mathieupommery/LABUBU_IA/HARDWARE/PCB/LIB_KIKAD/libloader/SM10B-SRSS-TB_LF__SN_.stp

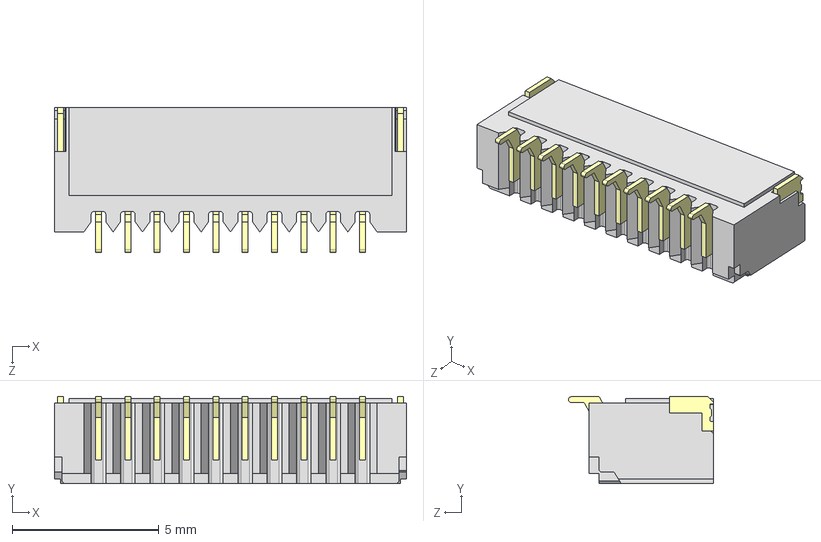
[picture p16: CAD file, 2025-12-20]
HARDWARE/PCB/LIB_KIKAD/libloader/SM10B-SRSS-TB_LF__SN_.stp
12.0 x 2.97 x 4.95 mm
