mathieupommery/LABUBU_IA/HARDWARE/PCB/LIB_KIKAD/libloader/TLE5012BE3005XUMA1.stp

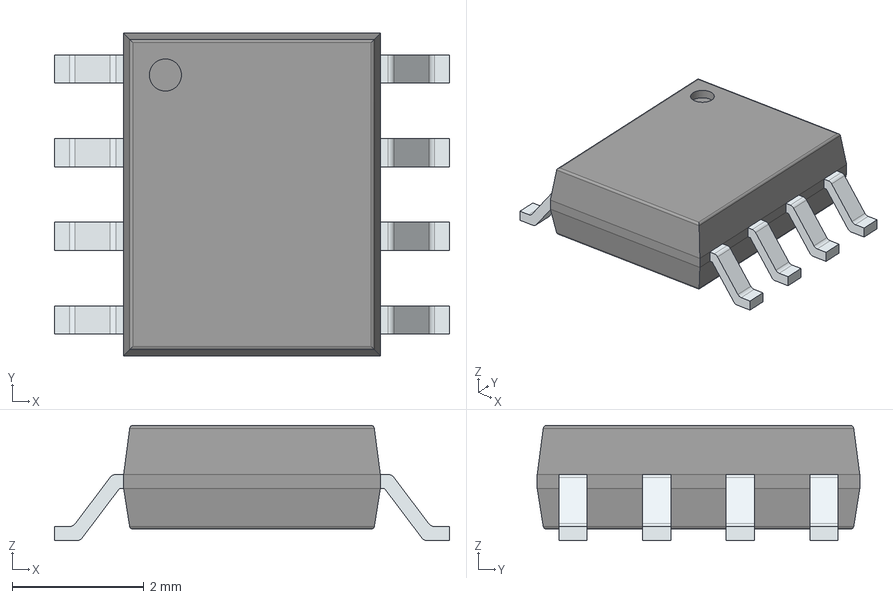
[picture p17: CAD file, 2025-12-20]
HARDWARE/PCB/LIB_KIKAD/libloader/TLE5012BE3005XUMA1.stp
6.00 x 4.90 x 1.75 mm
PinsArrayLR
