mathieupommery/LABUBU_IA/HARDWARE/PCB/LIB_KIKAD/libloader/ESP32-S3FH4R2.stp

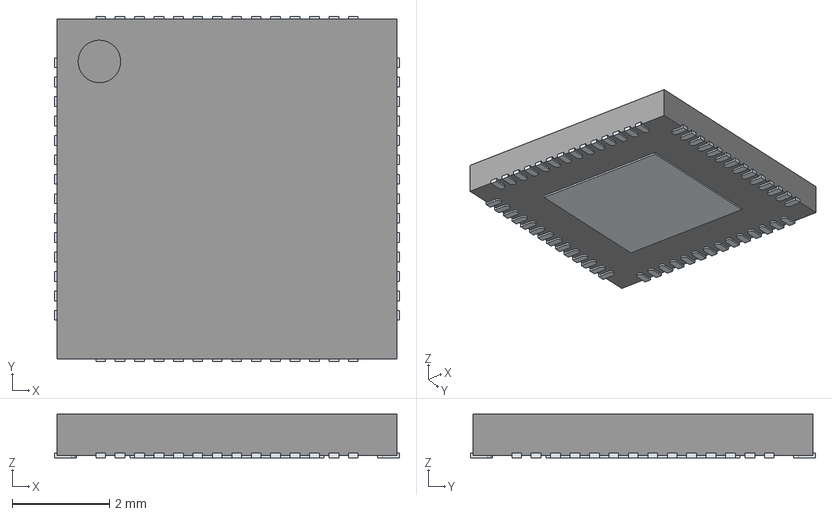
[picture p18: CAD file, 2025-12-20]
HARDWARE/PCB/LIB_KIKAD/libloader/ESP32-S3FH4R2.stp
7.10 x 7.10 x 0.9 mm
ThermalPin
PinsArrayLR
PinsArrayTB
