mathieupommery/LABUBU_IA/HARDWARE/PCB/LIB_KIKAD/libloader/XT30PW-M.stp

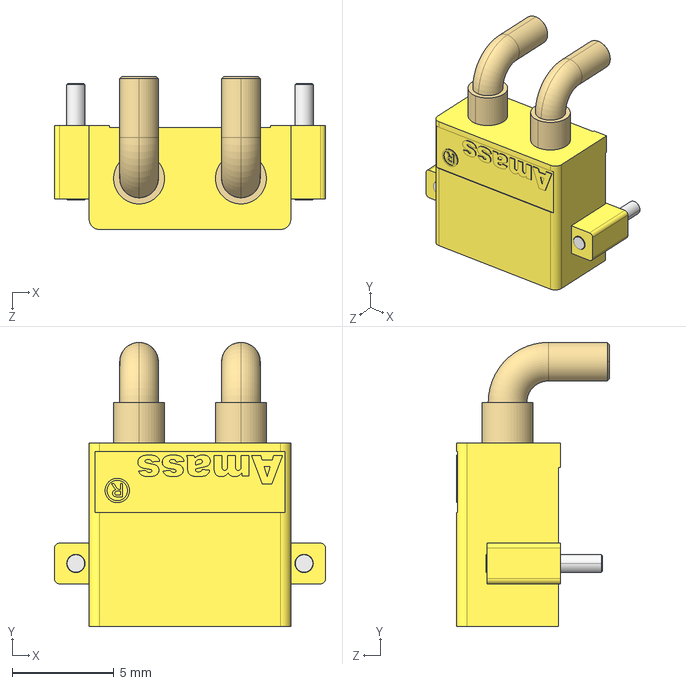
[picture p19: CAD file, 2025-12-20]
HARDWARE/PCB/LIB_KIKAD/libloader/XT30PW-M.stp
13.3 x 13.9 x 7.50 mm
