mathieupommery/LABUBU_IA/HARDWARE/PCB/LIB_KIKAD/libloader/MA330GQ-Z.stp

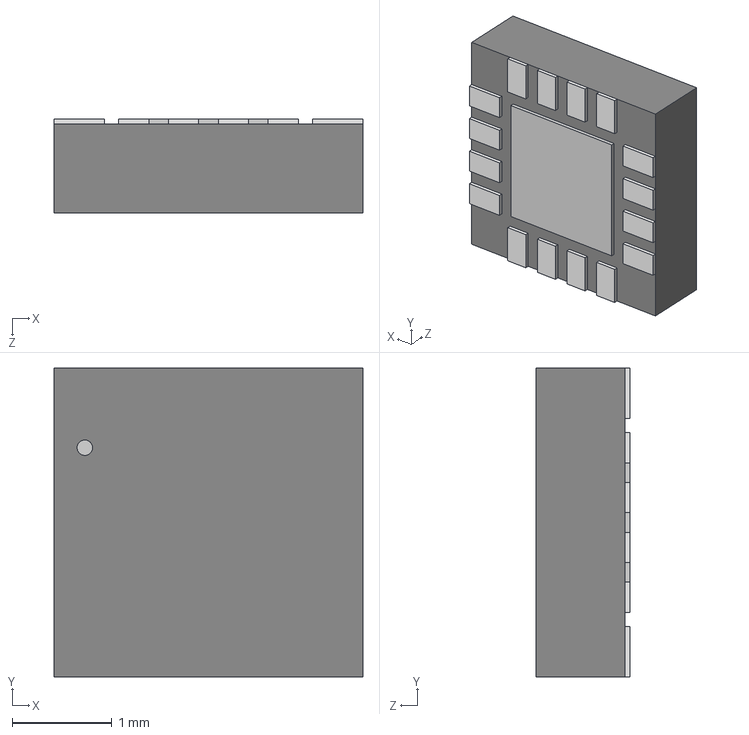
[picture p20: CAD file, 2025-12-20]
HARDWARE/PCB/LIB_KIKAD/libloader/MA330GQ-Z.stp
3.10 x 3.10 x 0.942 mm
