mathieupommery/LABUBU_IA/HARDWARE/PCB/LIB_KIKAD/libloader/BSS138PW.stp

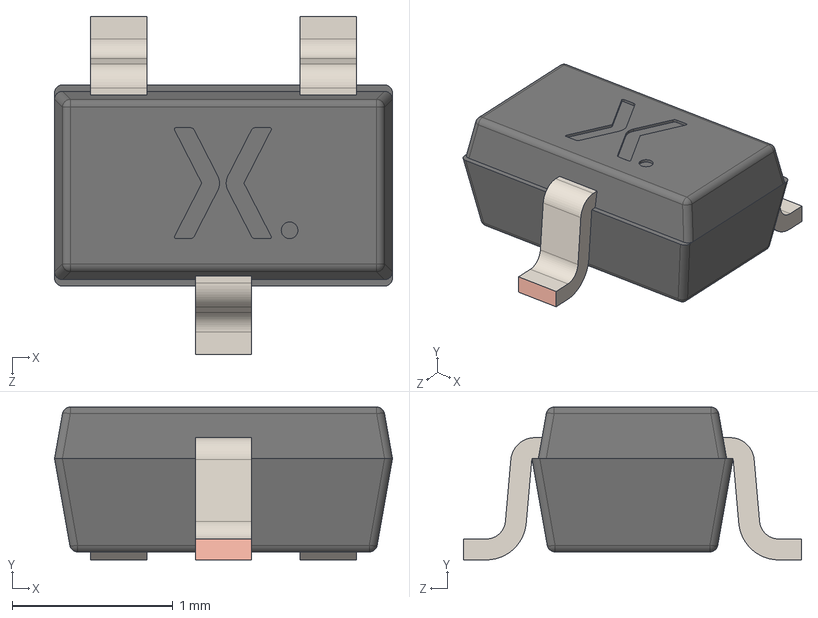
[picture p21: CAD file, 2025-12-20]
HARDWARE/PCB/LIB_KIKAD/libloader/BSS138PW.stp
2.10 x 0.95 x 2.10 mm
Upper body
lower body
Lead x 3
