mathieupommery/LABUBU_IA/HARDWARE/PCB/LIB_KIKAD/libloader/SM05B-GHS-TB_LF__SN_.stp

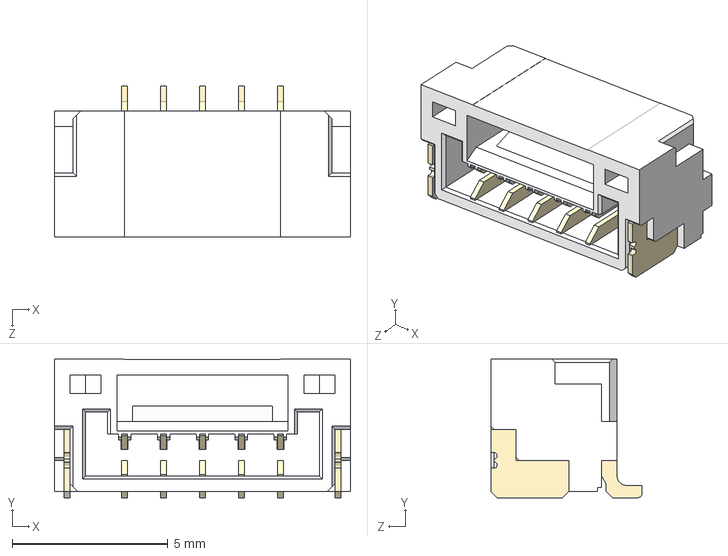
[picture p22: CAD file, 2025-12-20]
HARDWARE/PCB/LIB_KIKAD/libloader/SM05B-GHS-TB_LF__SN_.stp
9.50 x 4.45 x 4.85 mm
