mathieupommery/LABUBU_IA/HARDWARE/PCB/LIB_KIKAD/libloader/TPSM828214SILR.stp

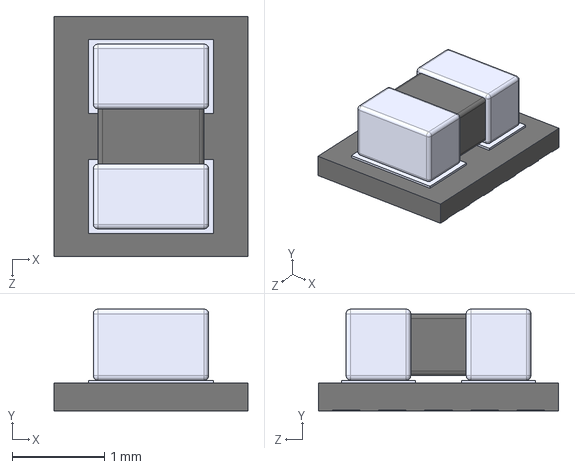
[picture p23: CAD file, 2025-12-20]
HARDWARE/PCB/LIB_KIKAD/libloader/TPSM828214SILR.stp
2.10 x 1.10 x 2.60 mm
