mathieupommery/LABUBU_IA/HARDWARE/PCB/LIB_KIKAD/libloader/HMC5883L-TR.stp

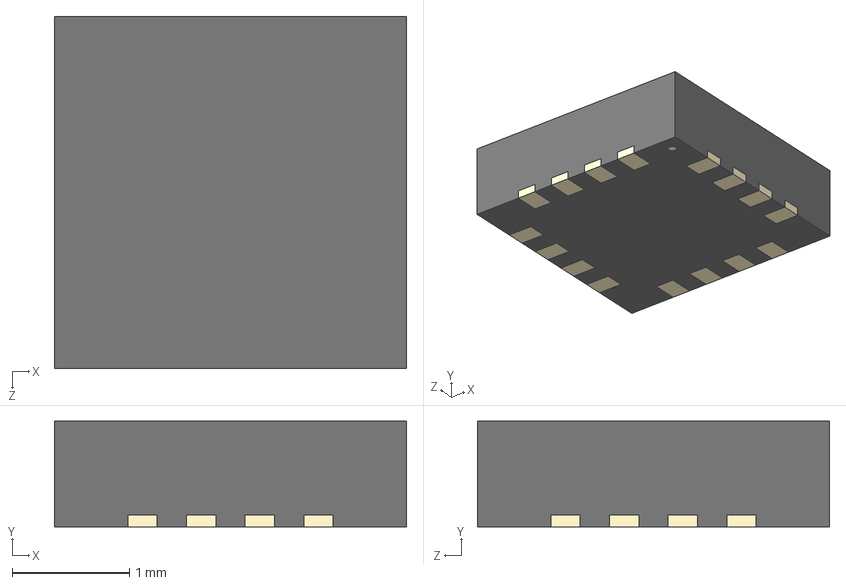
[picture p24: CAD file, 2025-12-20]
HARDWARE/PCB/LIB_KIKAD/libloader/HMC5883L-TR.stp
3.00 x 0.9 x 3.00 mm
