mathieupommery/LABUBU_IA/HARDWARE/PCB/LIB_KIKAD/libloader/LFXTAL069527REEL.stp

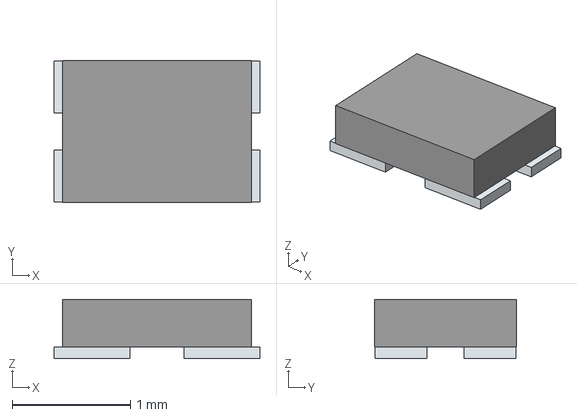
[picture p25: CAD file, 2025-12-20]
HARDWARE/PCB/LIB_KIKAD/libloader/LFXTAL069527REEL.stp
1.74 x 1.20 x 0.5 mm
Pins
