mathieupommery/LABUBU_IA/HARDWARE/PCB/LIB_KIKAD/libloader/LM2775DSGT.stp

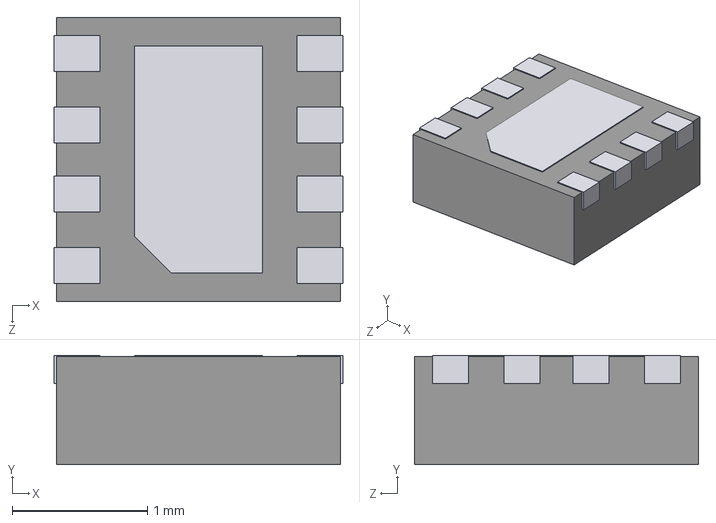
[picture p26: CAD file, 2025-12-20]
HARDWARE/PCB/LIB_KIKAD/libloader/LM2775DSGT.stp
2.14 x 0.81 x 2.10 mm
