mathieupommery/LABUBU_IA/HARDWARE/PCB/LIB_KIKAD/libloader/MAX-M10S-00B.stp

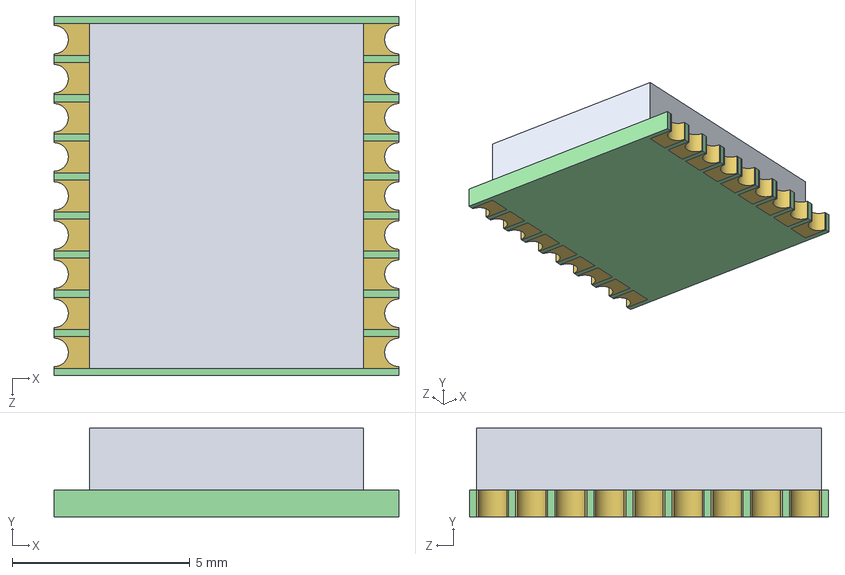
[picture p27: CAD file, 2025-12-20]
HARDWARE/PCB/LIB_KIKAD/libloader/MAX-M10S-00B.stp
9.70 x 2.50 x 10.1 mm
