mathieupommery/LABUBU_IA/HARDWARE/PCB/LIB_KIKAD/libloader/XT60PW-M.stp

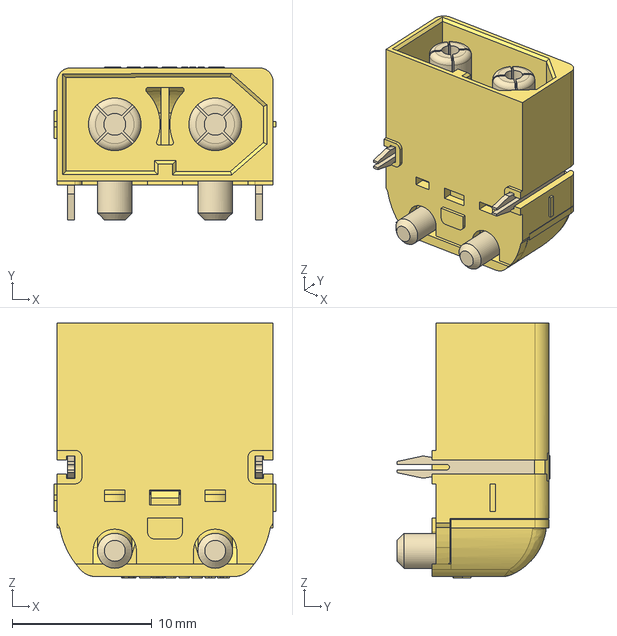
[picture p28: CAD file, 2025-12-20]
HARDWARE/PCB/LIB_KIKAD/libloader/XT60PW-M.stp
15.9 x 10.9 x 18.3 mm
