mathieupommery/LABUBU_IA/HARDWARE/PCB/LIB_KIKAD/libloader/MPX1D1264L4R7.stp

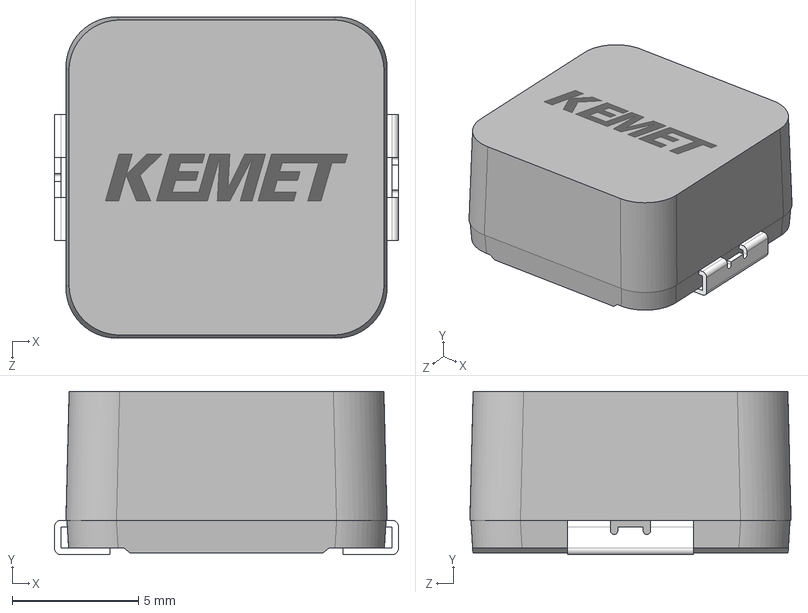
[picture p29: CAD file, 2025-12-20]
HARDWARE/PCB/LIB_KIKAD/libloader/MPX1D1264L4R7.stp
13.6 x 6.46 x 12.7 mm
