mathieupommery/LABUBU_IA/HARDWARE/PCB/LIB_KIKAD/libloader/STM32G071G8U6.stp

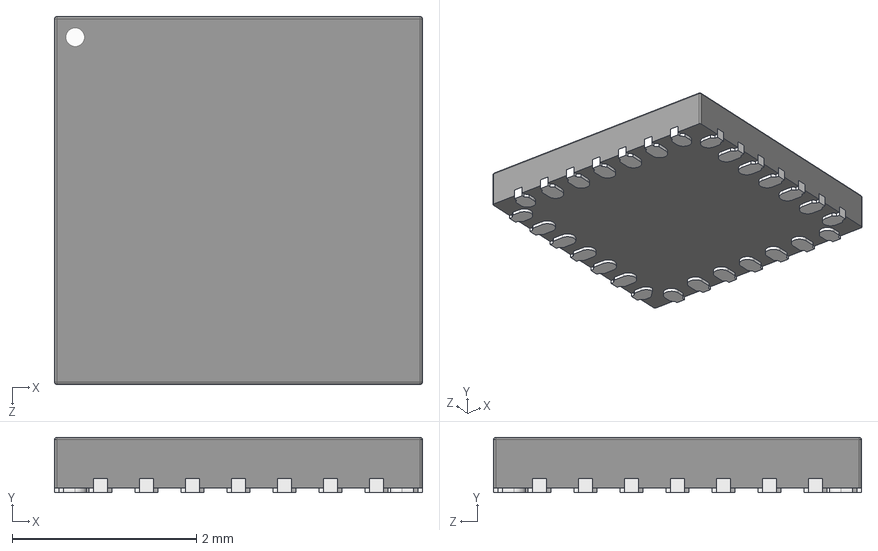
[picture p30: CAD file, 2025-12-20]
HARDWARE/PCB/LIB_KIKAD/libloader/STM32G071G8U6.stp
4.00 x 0.601 x 4.00 mm
