mathieupommery/LABUBU_IA/HARDWARE/PCB/LIB_KIKAD/libloader/SQS401EN-T1_BE3.stp

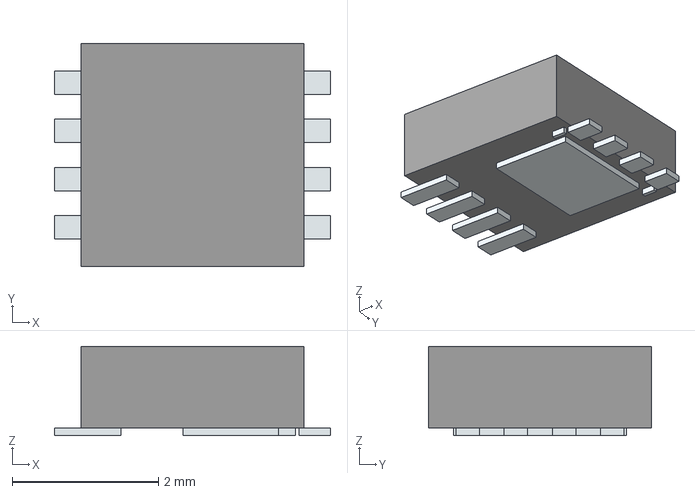
[picture p31: CAD file, 2025-12-20]
HARDWARE/PCB/LIB_KIKAD/libloader/SQS401EN-T1_BE3.stp
3.78 x 3.05 x 1.22 mm
Pins
