mathieupommery/LABUBU_IA/HARDWARE/PCB/LIB_KIKAD/libloader/W25Q16JWXHIQ_TR.stp

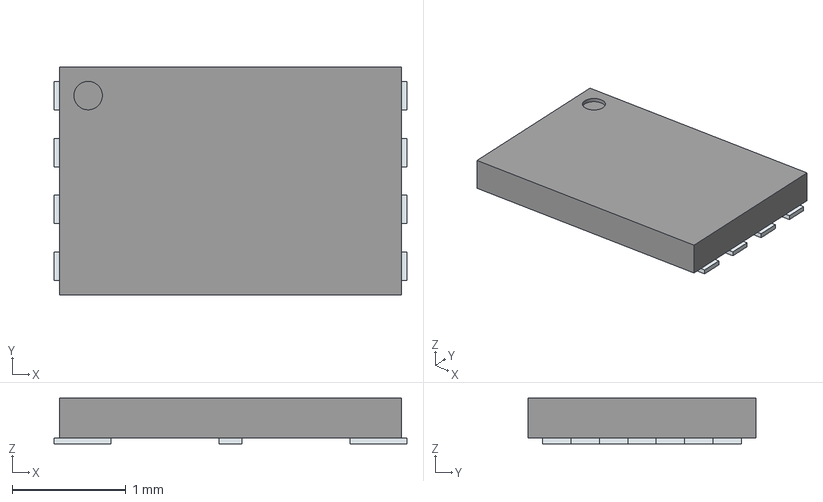
[picture p32: CAD file, 2025-12-20]
HARDWARE/PCB/LIB_KIKAD/libloader/W25Q16JWXHIQ_TR.stp
3.10 x 2.00 x 0.4 mm
ThermalPin
PinsArrayLR
