mathieupommery/LABUBU_IA/HARDWARE/PCB/LIB_KIKAD/libloader/STSPIN32G0A2.stp

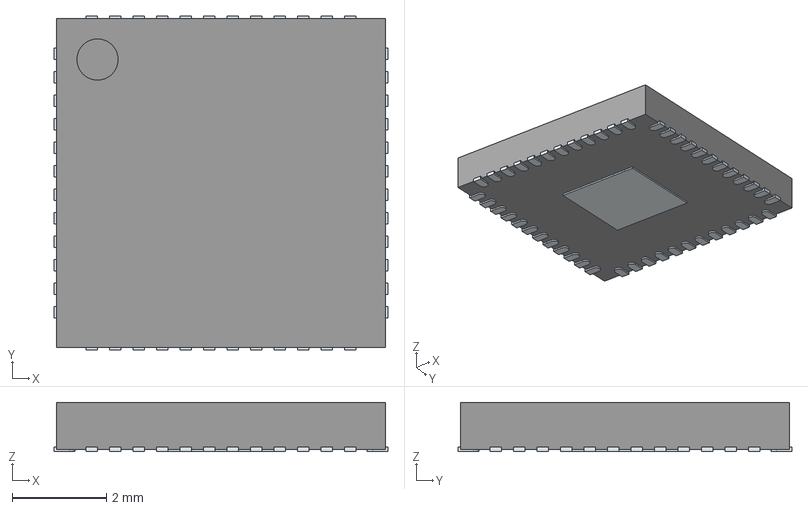
[picture p33: CAD file, 2025-12-20]
HARDWARE/PCB/LIB_KIKAD/libloader/STSPIN32G0A2.stp
7.10 x 7.10 x 1.05 mm
ThermalPin
PinsArrayLR
PinsArrayTB
