mathieupommery/LABUBU_IA/HARDWARE/PCB/LIB_KIKAD/libloader/CSTNE8M00GH5C000R0.stp

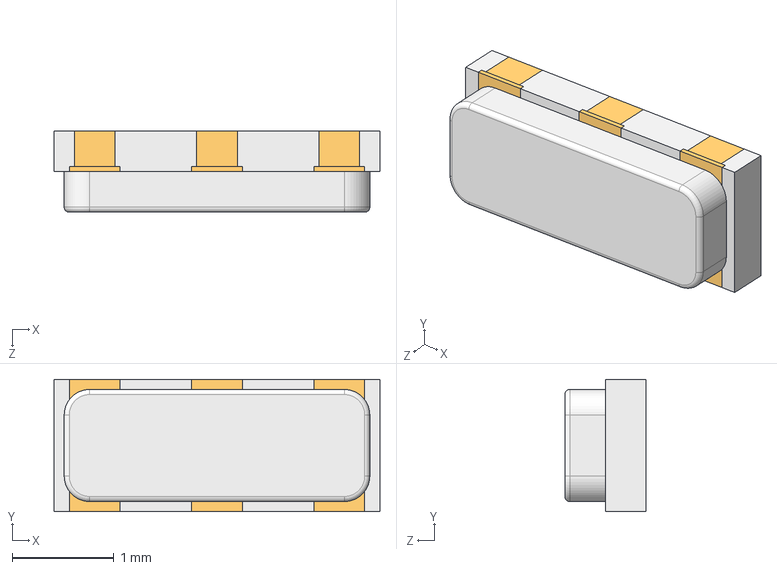
[picture p34: CAD file, 2025-12-20]
HARDWARE/PCB/LIB_KIKAD/libloader/CSTNE8M00GH5C000R0.stp
3.20 x 1.30 x 0.8 mm
