mathieupommery/LABUBU_IA/HARDWARE/PCB/LIB_KIKAD/libloader/TS5A3159ADCKR.stp

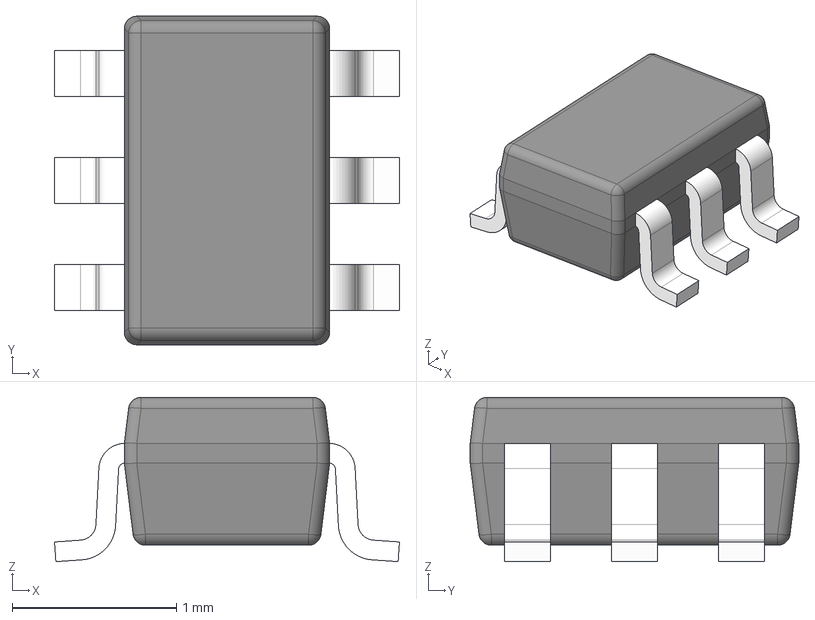
[picture p35: CAD file, 2025-12-20]
HARDWARE/PCB/LIB_KIKAD/libloader/TS5A3159ADCKR.stp
2.10 x 2.00 x 1.00 mm
BODY-SOT
LEAD-SOT x 6
PIN1-ID
