mathieupommery/LABUBU_IA/HARDWARE/PCB/LIB_KIKAD/libloader/STR2N2VH5.stp

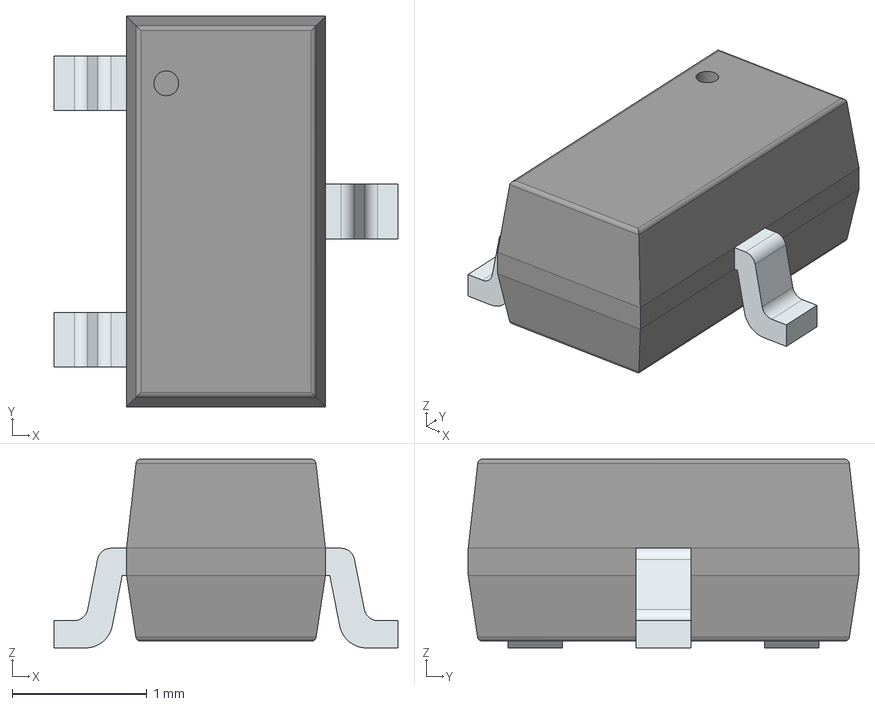
[picture p36: CAD file, 2025-12-20]
HARDWARE/PCB/LIB_KIKAD/libloader/STR2N2VH5.stp
2.55 x 2.90 x 1.40 mm
PinsArrayL
FilletPinR
