mathieupommery/LABUBU_IA/HARDWARE/PCB/LIB_KIKAD/libloader/DMT6018LDR-7.stp

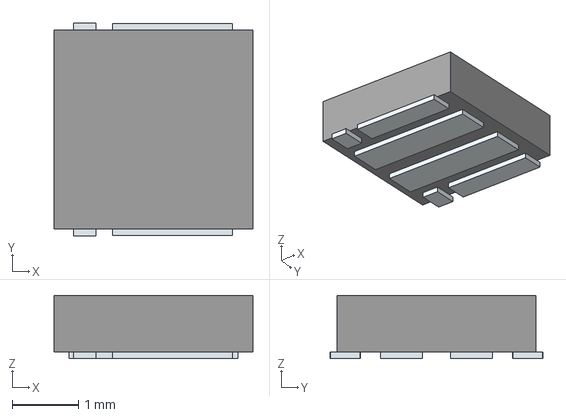
[picture p37: CAD file, 2025-12-20]
HARDWARE/PCB/LIB_KIKAD/libloader/DMT6018LDR-7.stp
3.00 x 3.22 x 0.95 mm
Pins
