mathieupommery/LABUBU_IA/HARDWARE/PCB/LIB_KIKAD/libloader/BAT60JFILM.stp

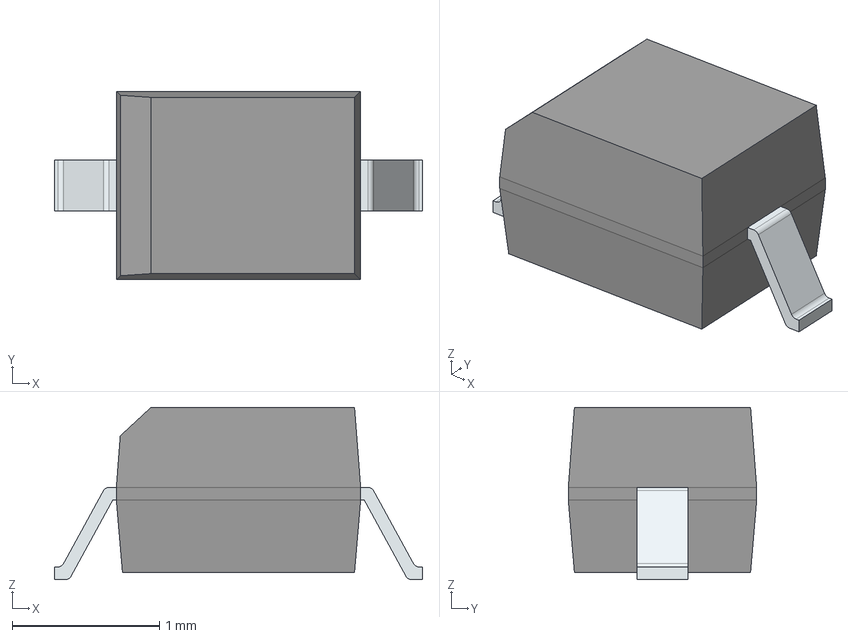
[picture p38: CAD file, 2025-12-20]
HARDWARE/PCB/LIB_KIKAD/libloader/BAT60JFILM.stp
2.50 x 1.28 x 1.17 mm
FilletPinL
FilletPinR
