mathieupommery/LABUBU_IA/HARDWARE/PCB/LIB_KIKAD/libloader/SM02B-GHS-TB_LF__SN_.stp

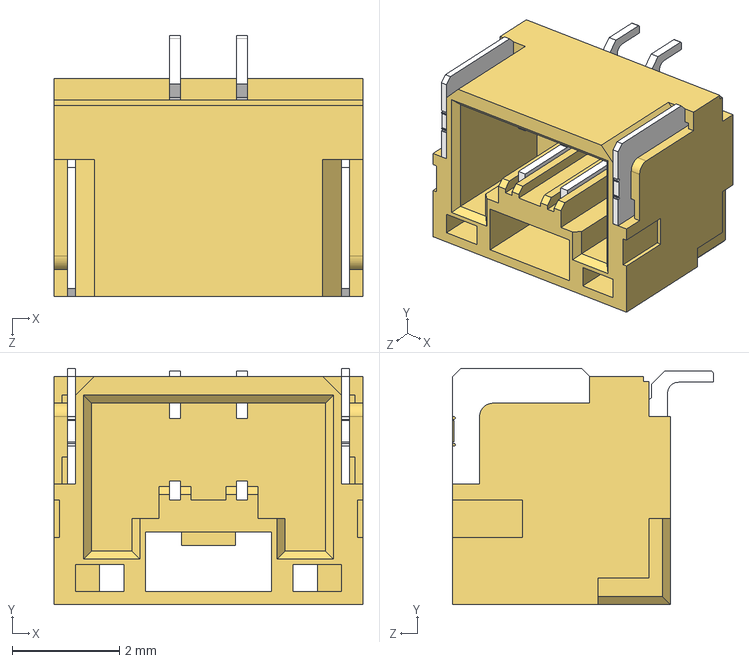
[picture p39: CAD file, 2025-12-20]
HARDWARE/PCB/LIB_KIKAD/libloader/SM02B-GHS-TB_LF__SN_.stp
5.75 x 4.40 x 4.85 mm
