mathieupommery/LABUBU_IA/HARDWARE/PCB/LIB_KIKAD/libloader/DPS368XTSA1.stp

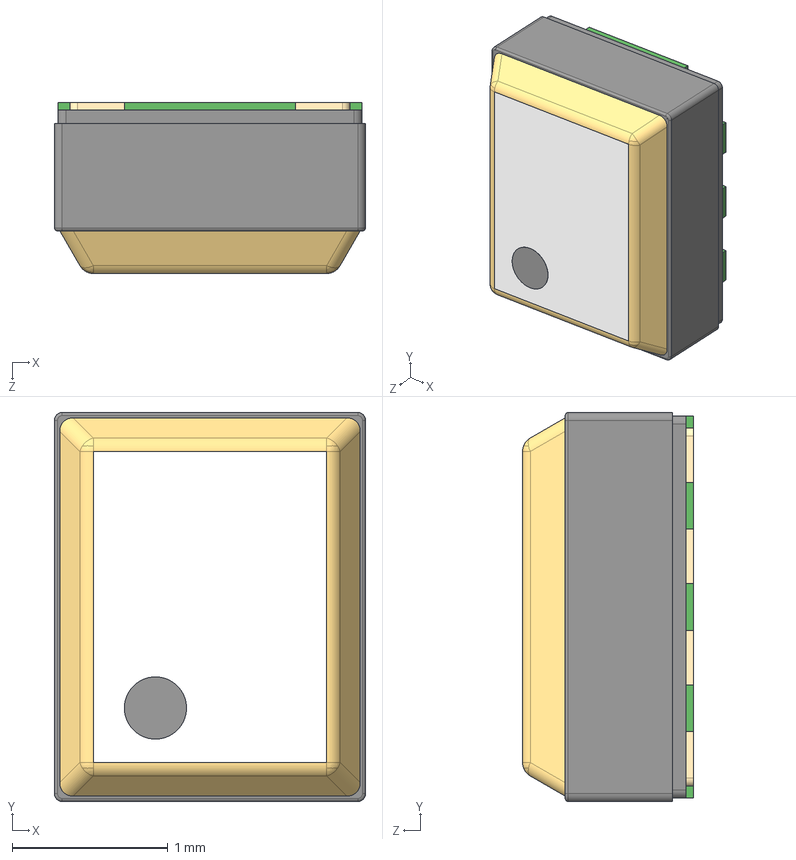
[picture p40: CAD file, 2025-12-20]
HARDWARE/PCB/LIB_KIKAD/libloader/DPS368XTSA1.stp
2.00 x 2.50 x 1.10 mm
Notch
Infineon Logo Adjustable_5
