mathieupommery/LABUBU_IA/HARDWARE/PCB/LIB_KIKAD/libloader/NC7WZ07P6X.stp

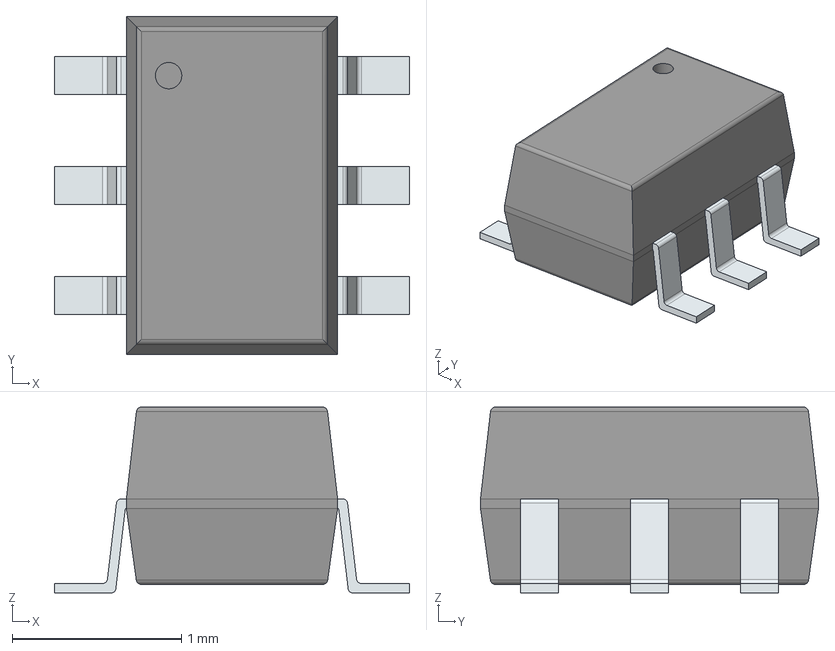
[picture p41: CAD file, 2025-12-20]
HARDWARE/PCB/LIB_KIKAD/libloader/NC7WZ07P6X.stp
2.10 x 2.00 x 1.10 mm
PinsArrayLR
