mathieupommery/LABUBU_IA/HARDWARE/PCB/LIB_KIKAD/libloader/STG719STR.stp

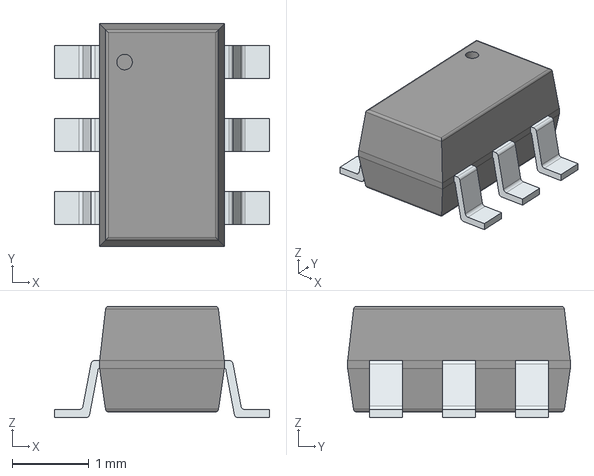
[picture p42: CAD file, 2025-12-20]
HARDWARE/PCB/LIB_KIKAD/libloader/STG719STR.stp
2.80 x 2.90 x 1.45 mm
PinsArrayLR
