mathieupommery/LABUBU_IA/HARDWARE/PCB/LIB_KIKAD/libloader/ESP32-C6FH4.stp

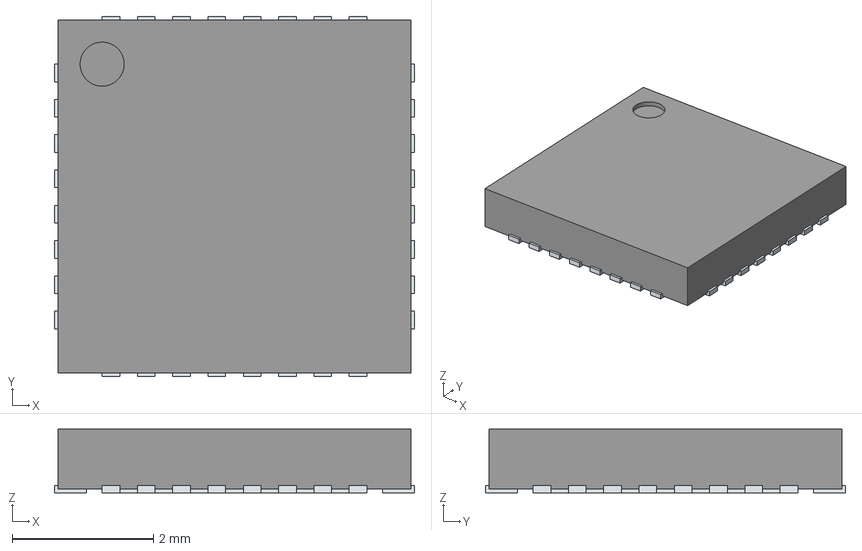
[picture p43: CAD file, 2025-12-20]
HARDWARE/PCB/LIB_KIKAD/libloader/ESP32-C6FH4.stp
5.10 x 5.10 x 0.9 mm
ThermalPin
PinsArrayLR
PinsArrayTB
