mathieupommery/LABUBU_IA/HARDWARE/PCB/LIB_KIKAD/libloader/RCLAMP3521ZATFT.stp

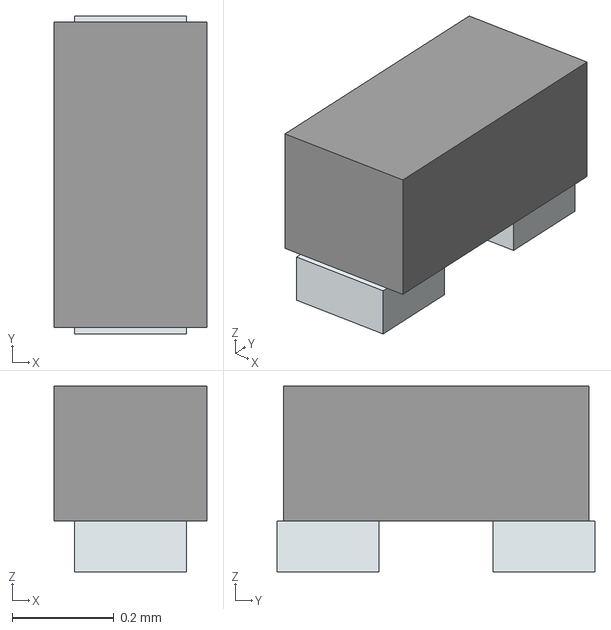
[picture p44: CAD file, 2025-12-20]
HARDWARE/PCB/LIB_KIKAD/libloader/RCLAMP3521ZATFT.stp
0.3 x 0.625 x 0.365 mm
Pins
