mathieupommery/LABUBU_IA/HARDWARE/PCB/LIB_KIKAD/libloader/SM12B-SRSS-TB_LF__SN_.stp

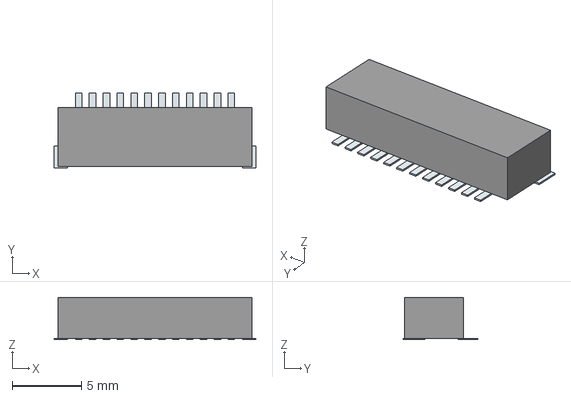
[picture p45: CAD file, 2025-12-20]
HARDWARE/PCB/LIB_KIKAD/libloader/SM12B-SRSS-TB_LF__SN_.stp
14.6 x 5.37 x 3.05 mm
Pins
