mathieupommery/LABUBU_IA/HARDWARE/PCB/LIB_KIKAD/libloader/W25N01GVZEIT.stp

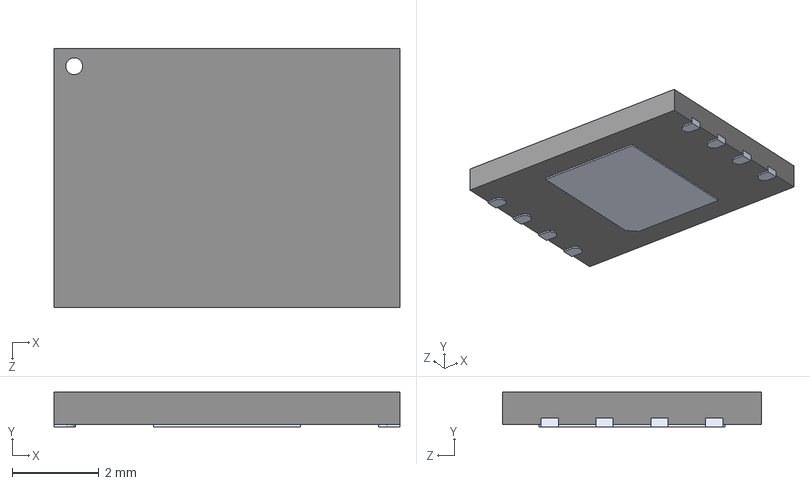
[picture p46: CAD file, 2025-12-20]
HARDWARE/PCB/LIB_KIKAD/libloader/W25N01GVZEIT.stp
8.00 x 0.8 x 6.00 mm
