mathieupommery/LABUBU_IA/HARDWARE/PCB/LIB_KIKAD/libloader/LSM6DSV80XTR.stp

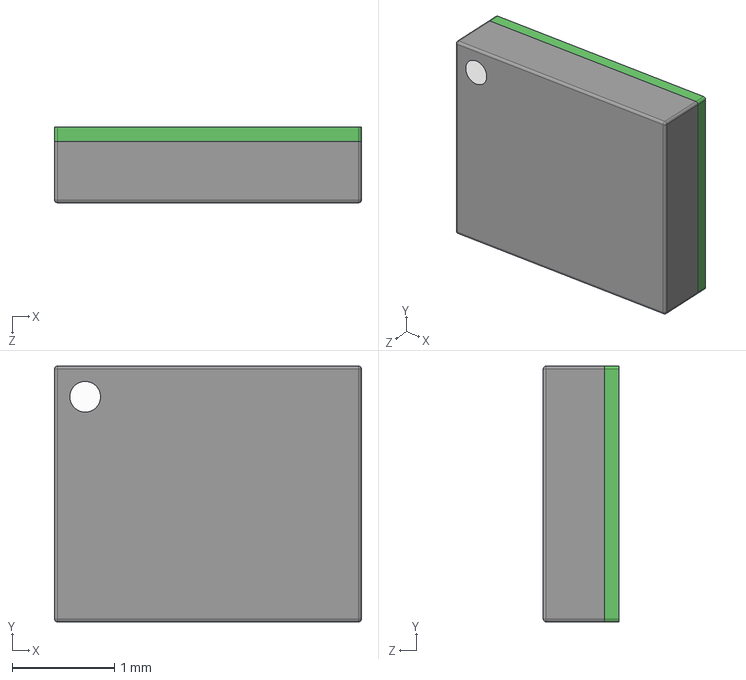
[picture p47: CAD file, 2025-12-20]
HARDWARE/PCB/LIB_KIKAD/libloader/LSM6DSV80XTR.stp
3.00 x 2.50 x 0.74 mm
