mathieupommery/LABUBU_IA/HARDWARE/PCB/LIB_KIKAD/libloader/LTC4065LEDC#TRMPBF.stp

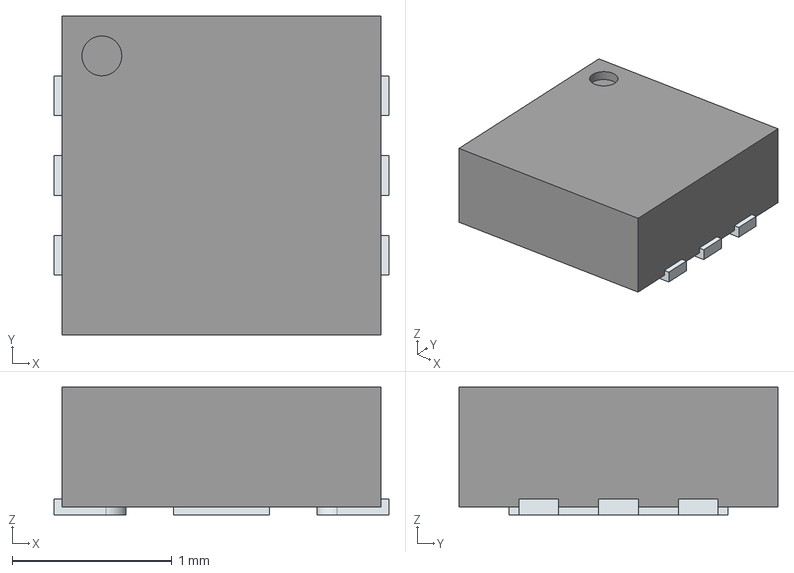
[picture p48: CAD file, 2025-12-20]
HARDWARE/PCB/LIB_KIKAD/libloader/LTC4065LEDC#TRMPBF.stp
2.10 x 2.00 x 0.8 mm
ThermalPin
PinsArrayLR
