mathieupommery/LABUBU_IA/HARDWARE/PCB/LIB_KIKAD/libloader/CHSA3920R0003F.stp

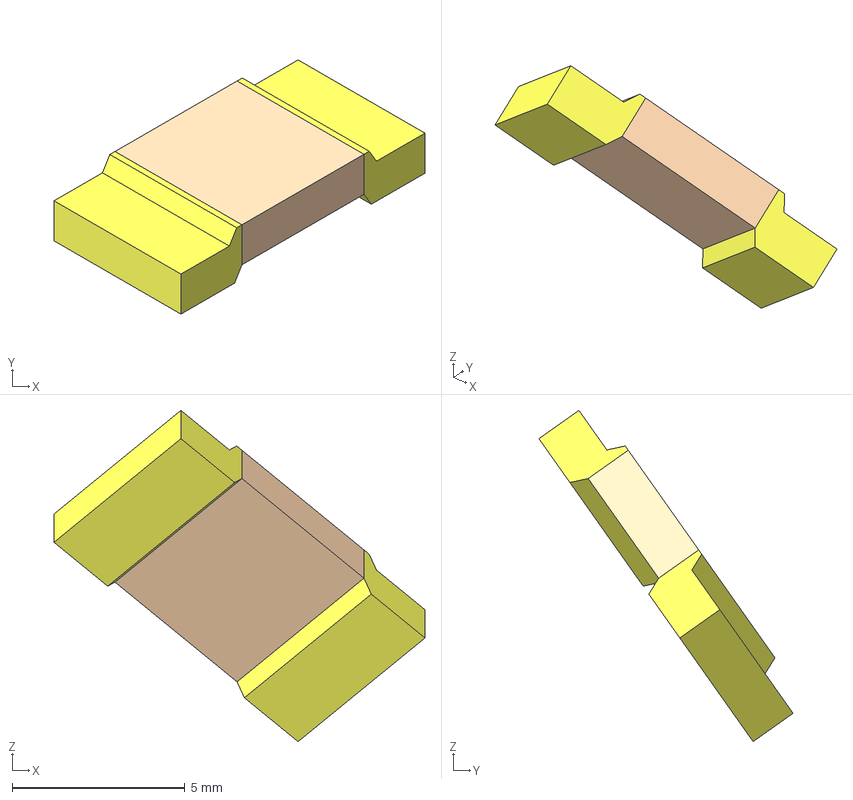
[picture p49: CAD file, 2025-12-20]
HARDWARE/PCB/LIB_KIKAD/libloader/CHSA3920R0003F.stp
10.7 x 7.36 x 9.60 mm
