mathieupommery/LABUBU_IA/HARDWARE/PCB/LIB_KIKAD/libloader/SIA527DJ-T1-GE3.stp

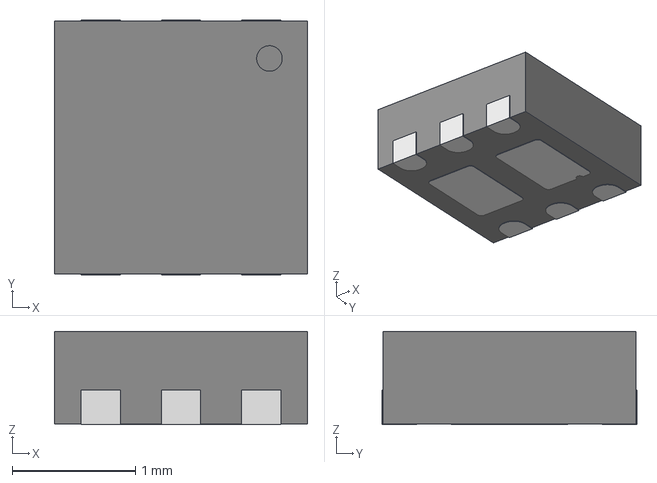
[picture p50: CAD file, 2025-12-20]
HARDWARE/PCB/LIB_KIKAD/libloader/SIA527DJ-T1-GE3.stp
2.05 x 2.07 x 0.757 mm
