mathieupommery/LABUBU_IA/HARDWARE/PCB/LIB_KIKAD/libloader/ICM-42688-P.stp

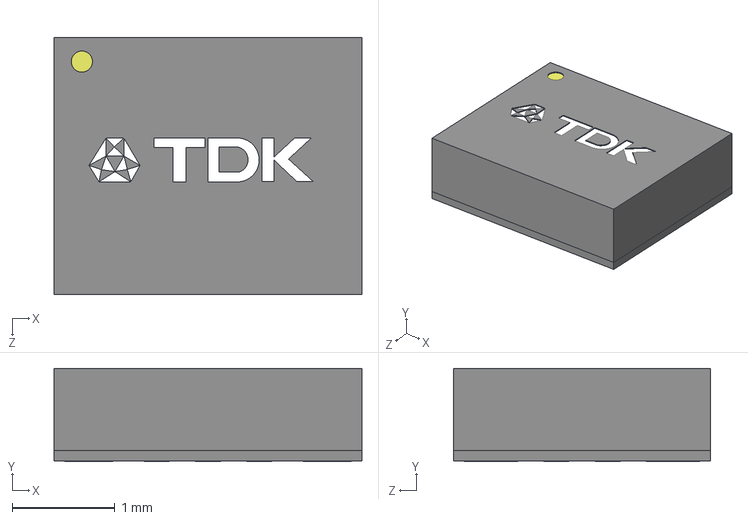
[picture p51: CAD file, 2025-12-20]
HARDWARE/PCB/LIB_KIKAD/libloader/ICM-42688-P.stp
3.00 x 0.91 x 2.50 mm
