mathieupommery/LABUBU_IA/HARDWARE/PCB/LIB_KIKAD/libloader/EMIF06-MSD02N16.stp

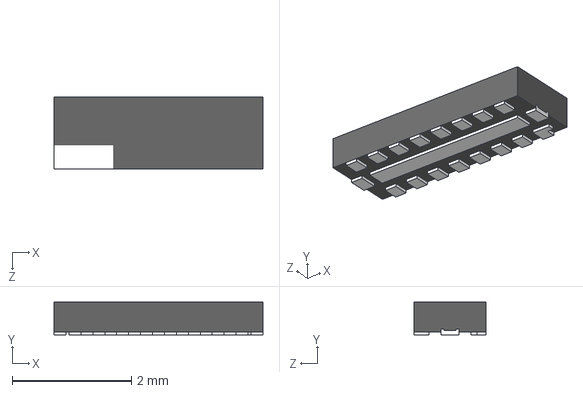
[picture p52: CAD file, 2025-12-20]
HARDWARE/PCB/LIB_KIKAD/libloader/EMIF06-MSD02N16.stp
3.50 x 0.55 x 1.20 mm
