mathieupommery/LABUBU_IA/HARDWARE/PCB/LIB_KIKAD/libloader/SF14-1582M5UUD2.stp

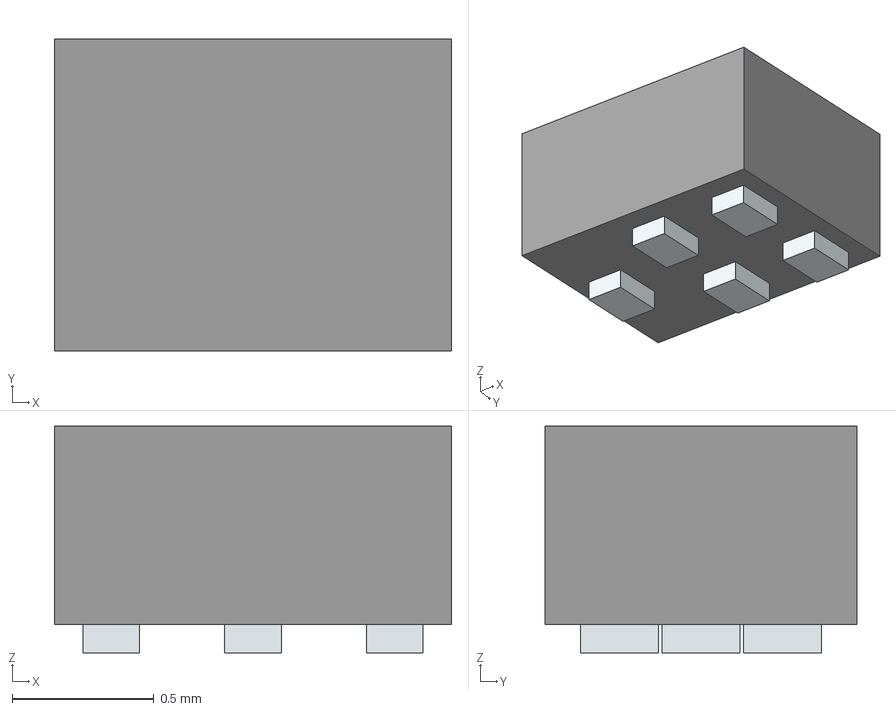
[picture p53: CAD file, 2025-12-20]
HARDWARE/PCB/LIB_KIKAD/libloader/SF14-1582M5UUD2.stp
1.40 x 1.10 x 0.8 mm
Pins
