mathieupommery/LABUBU_IA/HARDWARE/PCB/LIB_KIKAD/libloader/MIA-M10Q-00B.stp

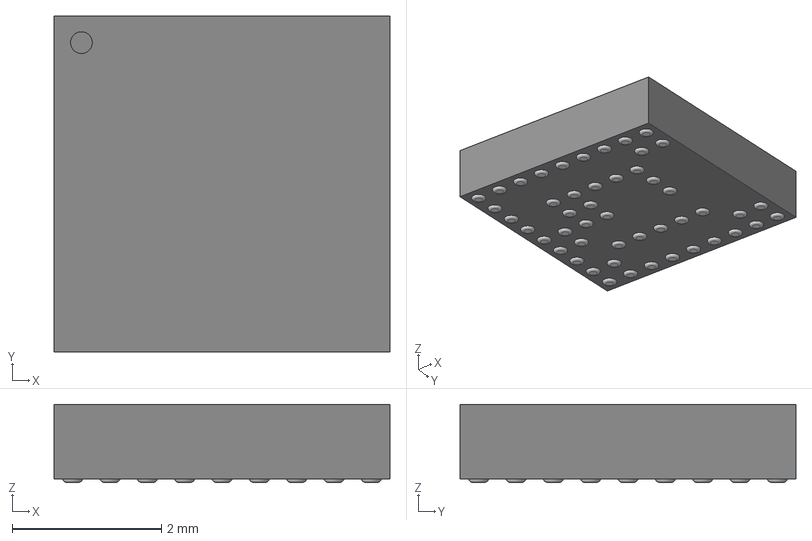
[picture p54: CAD file, 2025-12-20]
HARDWARE/PCB/LIB_KIKAD/libloader/MIA-M10Q-00B.stp
4.50 x 4.50 x 1.04 mm
