mathieupommery/LABUBU_IA/HARDWARE/PCB/LIB_KIKAD/libloader/BMP581.stp

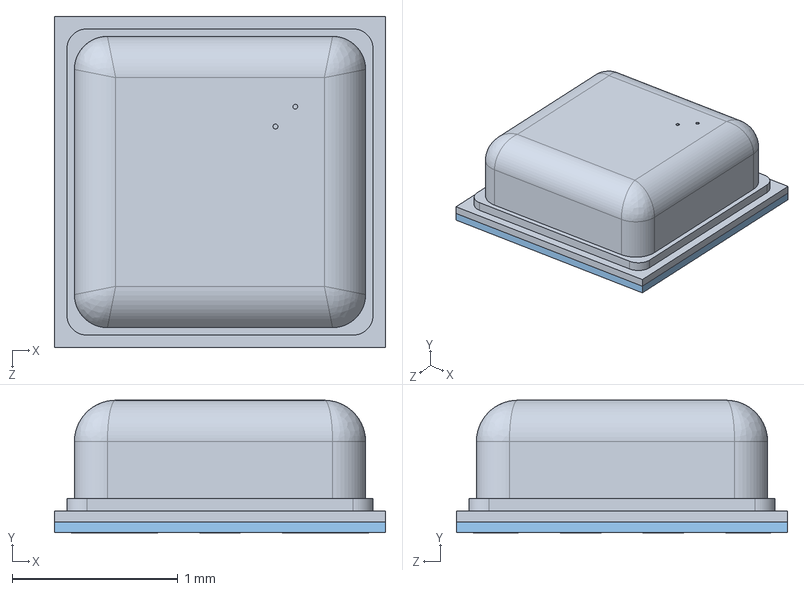
[picture p55: CAD file, 2025-12-20]
HARDWARE/PCB/LIB_KIKAD/libloader/BMP581.stp
2.00 x 0.801 x 2.00 mm
