mathieupommery/LABUBU_IA/HARDWARE/PCB/LIB_KIKAD/libloader/TPS3424A11C13ADRLR.stp

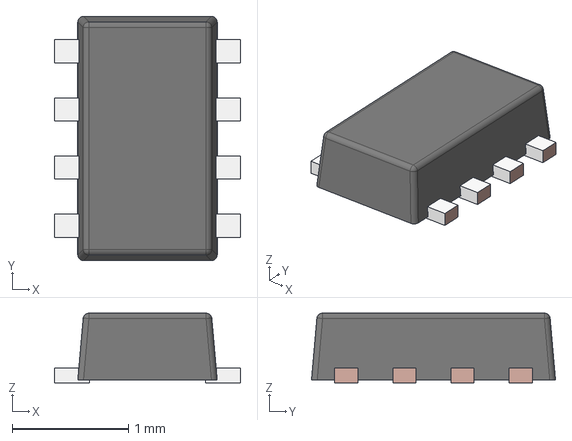
[picture p56: CAD file, 2025-12-20]
HARDWARE/PCB/LIB_KIKAD/libloader/TPS3424A11C13ADRLR.stp
1.60 x 2.10 x 0.6 mm
FRAME-DRL0008A
BODY-SOT
