mathieupommery/LABUBU_IA/HARDWARE/PCB/LIB_KIKAD/libloader/LTC2955CDDB-2#TRMPBF.stp

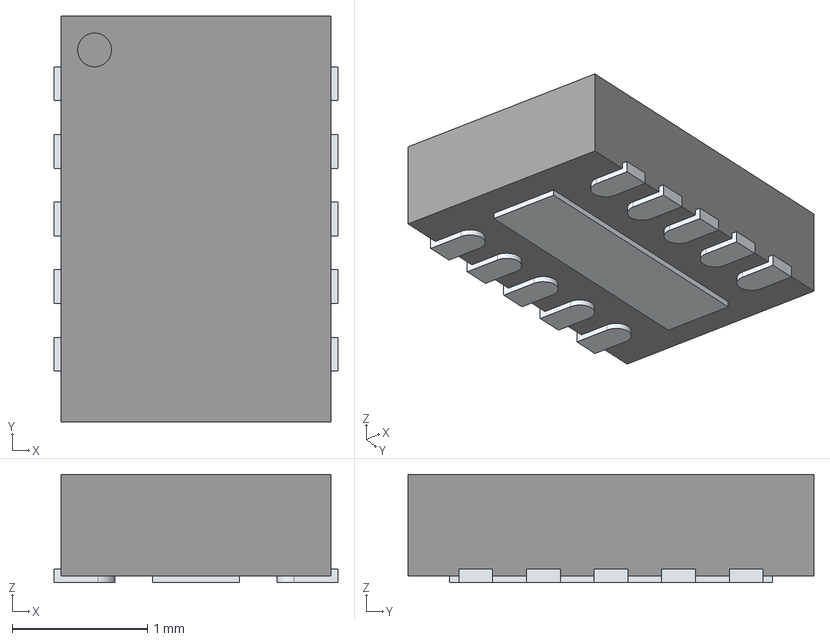
[picture p57: CAD file, 2025-12-20]
HARDWARE/PCB/LIB_KIKAD/libloader/LTC2955CDDB-2#TRMPBF.stp
2.10 x 3.00 x 0.8 mm
ThermalPin
PinsArrayLR
