mathieupommery/LABUBU_IA/HARDWARE/PCB/LIB_KIKAD/libloader/PTS845VM20PSMTR4_LFS.stp

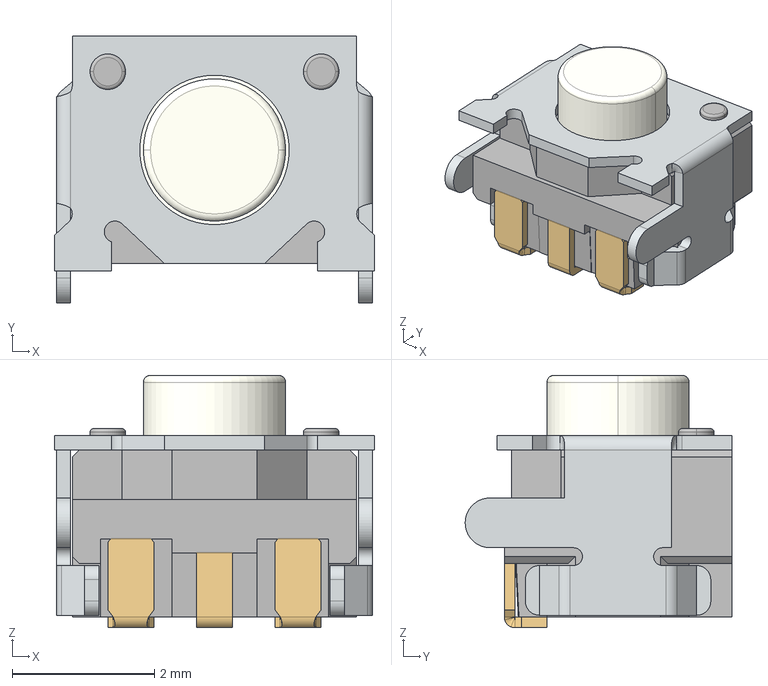
[picture p59: CAD file, 2025-12-20]
HARDWARE/PCB/LIB_KIKAD/libloader/PTS845VM20PSMTR4_LFS.stp
4.50 x 3.75 x 3.55 mm
