mathieupommery/LABUBU_IA/HARDWARE/PCB/LIB_KIKAD/libloader/PCM12SMTR.stp

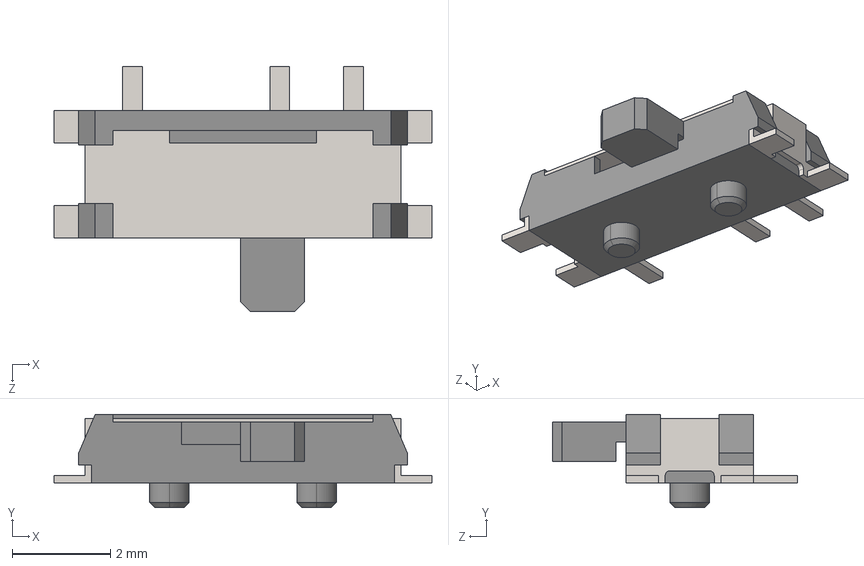
[picture p60: CAD file, 2025-12-20]
HARDWARE/PCB/LIB_KIKAD/libloader/PCM12SMTR.stp
7.70 x 1.90 x 5.00 mm
