mathieupommery/LABUBU_IA/HARDWARE/PCB/LIB_KIKAD/libloader/SM03B-GHS-TB_LF__SN_.stp

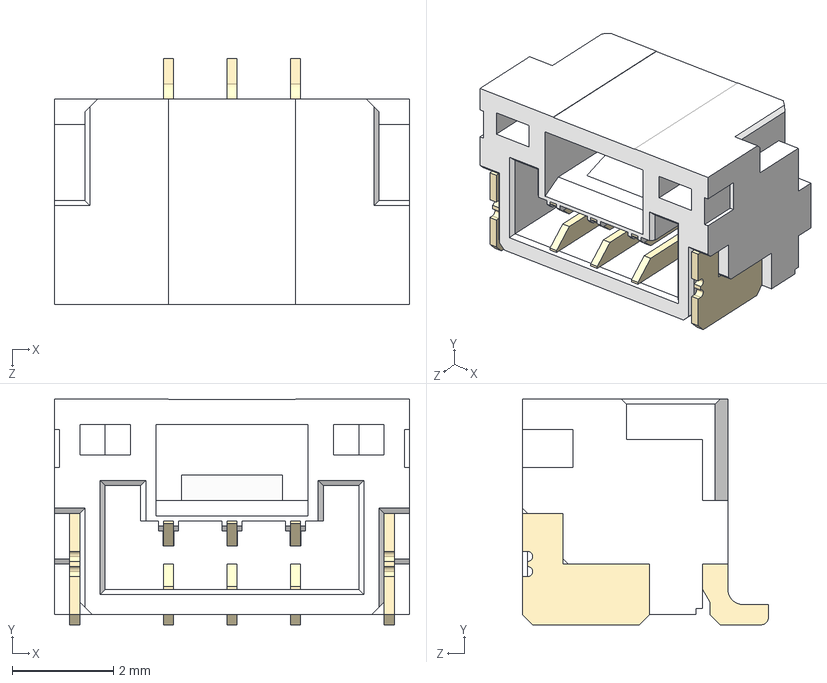
[picture p61: CAD file, 2025-12-20]
HARDWARE/PCB/LIB_KIKAD/libloader/SM03B-GHS-TB_LF__SN_.stp
7.00 x 4.45 x 4.85 mm
