mathieupommery/LABUBU_IA/HARDWARE/PCB/LIB_KIKAD/libloader/STPS0560Z.stp

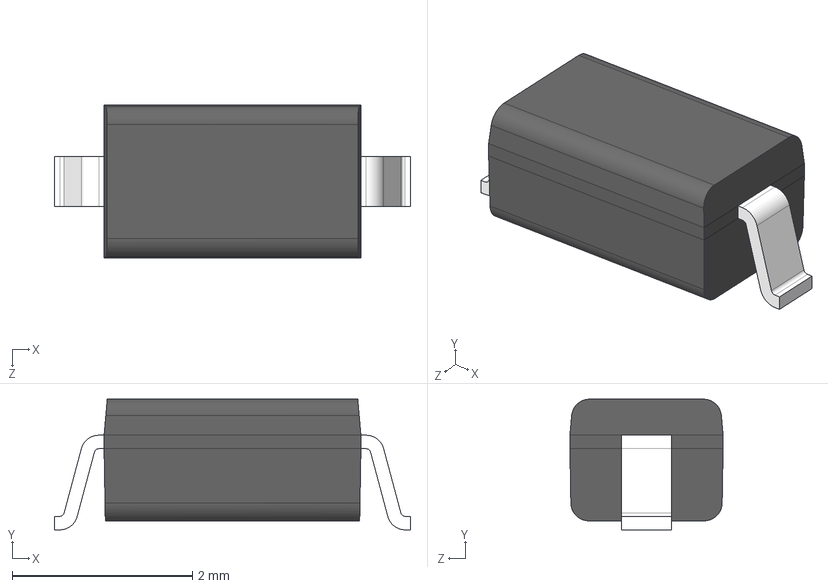
[picture p62: CAD file, 2025-12-20]
HARDWARE/PCB/LIB_KIKAD/libloader/STPS0560Z.stp
3.95 x 1.45 x 1.70 mm
