mathieupommery/LABUBU_IA/HARDWARE/PCB/LIB_KIKAD/libloader/USB4110-GF-A.stp

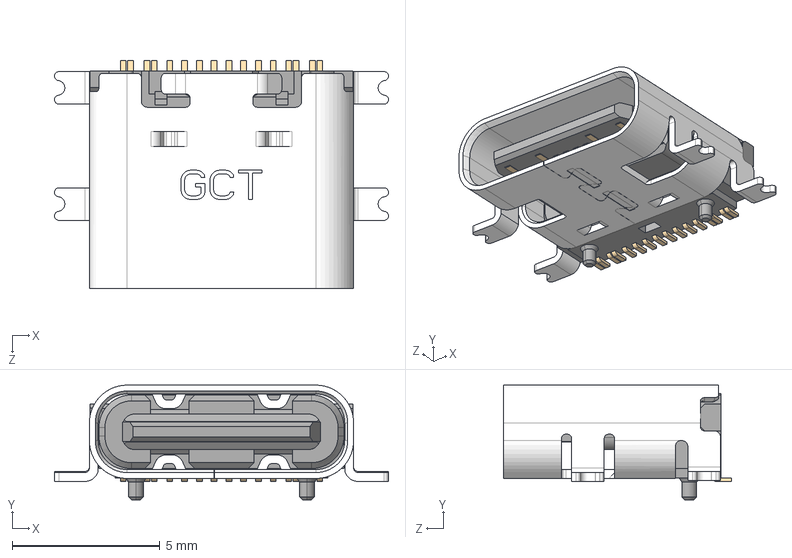
[picture p63: CAD file, 2025-12-20]
HARDWARE/PCB/LIB_KIKAD/libloader/USB4110-GF-A.stp
11.3 x 3.89 x 7.70 mm
