mathieupommery/LABUBU_IA/HARDWARE/PCB/LIB_KIKAD/libloader/TSC213ICT.stp

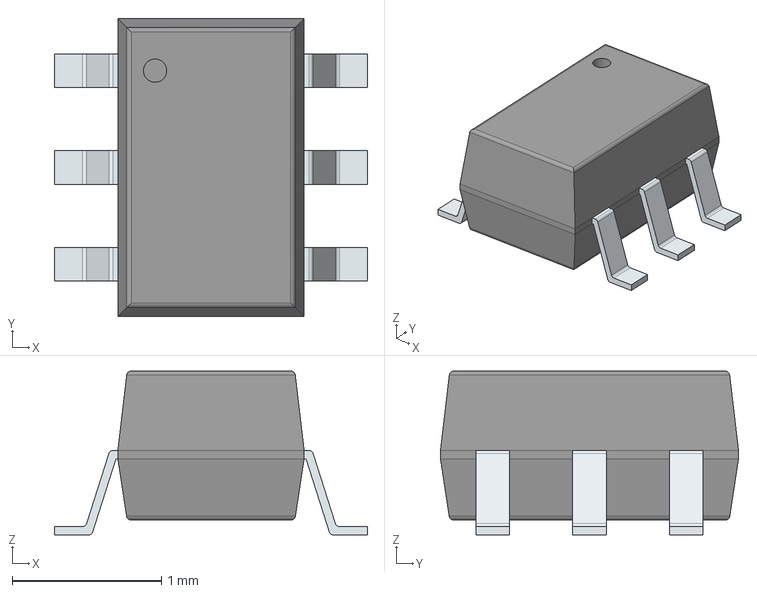
[picture p64: CAD file, 2025-12-20]
HARDWARE/PCB/LIB_KIKAD/libloader/TSC213ICT.stp
2.10 x 2.00 x 1.10 mm
PinsArrayLR
