mathieupommery/LABUBU_IA/HARDWARE/PCB/LIB_KIKAD/libloader/SM08B-SRSS-TB.stp

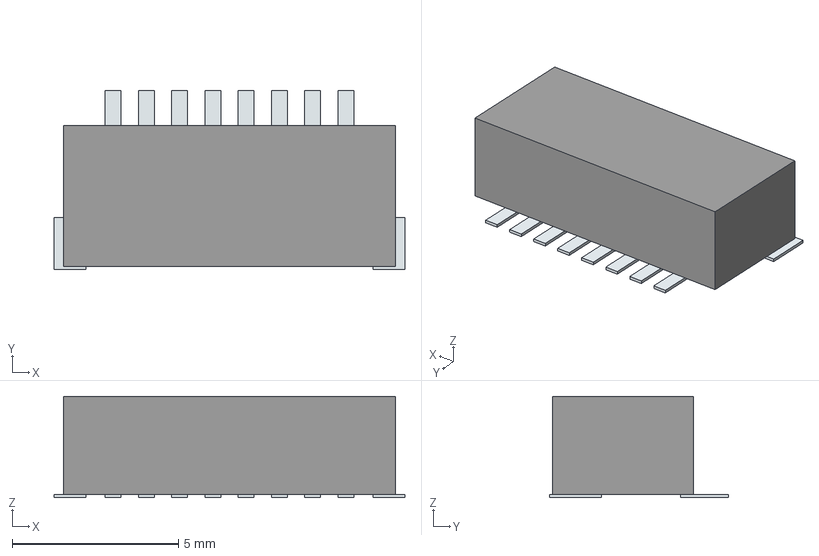
[picture p65: CAD file, 2025-12-20]
HARDWARE/PCB/LIB_KIKAD/libloader/SM08B-SRSS-TB.stp
10.6 x 5.37 x 3.05 mm
Pins
